MattMcC27/Analog-Synth/VCO new.asc

1k: res; 20k
C1: cap; 4.7n
C3: cap; 4.7n
C6: cap; 100p
D2: diode
D3: diode
Q1: npn
Q2: npn
Q3: npn
R1: res; 10k
R2: res; 10k
R3: res; 100k
R5: res; 200k
R6: res; 6.6k
R7: res; 15k
R8: res; 6.6k
R9: res; 4.7k
R10: res; 100k
R11: res; 100k
R12: res; 4.7k
R13: res; 10k
R14: res; 10k
R15: res; 50k
R16: res; 100k
R17: res; 10k
R18: res; 100k
R19: res; 100k
R20: res; 4Meg
R21: res; 100k
R22: res; 100k
R23: res; 2k
R24: res; 10k
R25: res; 500
R26: res; 500
R27: res; 3900
U1: OP07
U2: LT1011
U3: OP07
U4: OP07
U5: OP07
U6: OP07
U7: OP07
U8: OP07
U9: OP07
U10: OP07
U11: UniversalOpAmp
U13: UniversalOpAmp
U14: LT1011
U15: OP07
V1: voltage; 12
V2: voltage; 12
V3: voltage; 2.5
V4: voltage; 5
V5: voltage; 5
V6: voltage; -2.57
VCO: voltage; 2
Named nets: 0, -12, +12, +5, -5, Int_out, 5+, 5-, CV, Square, Tri
.tran 0.01 uic ;1 uic ; uic
.lib TL074.lib
